IsaacNudeton/FBC-Semiconductor-System/docs/GAPS.md

# FBC System Gaps — Updated March 28, 2026

**FIRMWARE FEATURE-COMPLETE.** All Sonoma gaps closed. 79 wire codes, 43 tests, 0 warnings. Needs single JTAG deploy.

---

## Status Summary

| Category | Working (code) | Broken | Untested (needs hardware) | Missing |
|---|---|---|---|---|
| Protocol commands | 56 operations / 79 wire codes | 0 | DDR slots + test plan + IO bank + min/max (all code-complete) | 0 |
| AXI peripherals | 8 of 8 | 0 | 0 | 0 |
| Sensors | XADC (39.5°C verified) + MIN_MAX tracking | 0 | MIN_MAX on hardware | 0 |
| Storage | SD guarded | 0 | 0 | 0 |
| Thermal | Full loop: NTC → PID → DAC → FET | 0 | DAC output on real heater | 0 |
| V×I Power | read_core_power_mw() → feedforward | 0 | Actual current readings | 0 |
| DNA / MAC | 00:0A:35:C6:B4:2A verified | 0 | 0 | 0 |
| DDR Slots | Code complete (388 lines) | 0 | Hardware upload + run | 0 |
| Test Plan | Code complete (647 lines) | 0 | Autonomous execution | 0 |
| Undervoltage | Safety check added | 0 | Trip on real sag | 0 |
| IO Bank | IO_BANK_SET handler | 0 | I2C addr verification | 0 |
| GUI | wgpu native, 14 panels, switch | 0 | 0 | 0 |

---

## WORKING (16 commands, live-tested March 24)

Full command sweep on calibration board (12V/3A, calibration BIM connected via J3/J4/J5, no 48V/LCPS/DUT, EEPROM never programmed):

| Command | What it does | Verified | Notes |
|---|---|---|---|
| discover | Finds board, returns MAC/serial/version | March 24 | MAC 00:0A:35:AD:00:02 |
| ping | Round-trip latency | March 24 | 1.5ms RTT |
| status | 47-byte telemetry (state, cycles, errors, temp) | March 24 | Temp wrong (XADC bug) |
| firmware-info | Version, build date, serial, hw rev | March 24 | v1.0.0, serial 00000002 |
| vector-status | Vector engine state from AXI registers | March 24 | Idle, 0 vectors/errors |
| errors | Error log from BRAM (8 entries) | March 24 | All zeroed (correct) |
| analog | 32-channel ADC readings | March 24 | All 0mV (no DUT, expected) |
| log-info | Flight recorder metadata | March 24 | SD not present, 0 entries |
| vicor | 6-core status (all disabled — no 48V) | March 24 | Correct for cal board |
| eeprom | Read (safe empty — BIM present but EEPROM never programmed) | March 24 | Empty, expected |
| fastpins read | Read fast pin state | March 24 | din/dout/oen = 0x00000000 |
| set-fastpins | Write fast pin output + OEN | March 24 | Wrote 0xDEADBEEF |
| fastpins readback | **Round-trip verified** | March 24 | dout=0xDEADBEEF, oen=0xFFFFFFFF |
| configure | ACK received (clock write disabled) | March 24 | See bug #1b below |
| emergency-stop | Immediate ack | March 24 | |
| stop | Disables FBC decoder | March 24 | |

---

## BROKEN — NONE (all previously broken items fixed)

### ~~1. CONFIGURE (0x30) — clk_ctrl AXI crash~~ — ✅ FIXED March 25

- **Root cause:** Incomplete `case` statements in `clk_ctrl.v` AXI write FSM — missing `default:` arms for unhandled address ranges
- **Fix:** Added `default: ;` to both write case statements in `clk_ctrl.v`
- **Verified on hardware:** `configure --clock 3` succeeds, board survives
- **Bitstream rebuilt** with full timing closure (WNS=+0.018ns)

### ~~2. PAUSE (0xB5) / RESUME (0xB6)~~ — ✅ FIXED

- **Status:** Fully implemented and dispatched
- `handle_pause()` at `fbc_protocol.rs:1503` — disables FBC decoder, sets state to Paused
- `handle_resume()` at `fbc_protocol.rs:1512` — enables FBC decoder, sets state to Running
- Dispatched at `fbc_protocol.rs:1291-1292`

### ~~2b. PMBUS_STATUS_REQ (0x84)~~ — ✅ FIXED March 24

- **Was:** Command silently dropped (falls through to `_ => None`)
- **Fix:** Added dispatch arm + `handle_pmbus_status_req()`. Sets `pending_pmbus_status` flag, main.rs polls it, calls `psu_mgr.update_telemetry()`, builds response with per-supply address/bus/on/vout/iout.

### ~~2c. Vector LOAD/START/STOP (0xB2/0xB4/0xB7)~~ — ✅ FIXED March 24

- **Was:** Commands silently dropped (fall through to `_ => None`)
- **Fix:** Added dispatch arms:
  - LOAD (0xB2): Returns LOAD_ACK with status=0xFF (not fully implemented — needs SD-cached vector support)
  - START (0xB4): Delegates to `handle_start()` (same as runtime::START 0x40)
  - STOP (0xB7): Delegates to `handle_stop()` (same as runtime::STOP 0x41)
- No more silent drops — all commands get responses now

### ~~3. XADC — returns wrong values~~ — ✅ FIXED and VERIFIED March 25

- **Root cause:** u32 arithmetic overflow in `xadc.rs:242`. `raw * 503975` overflows u32 for any raw > 8522. Fixed: `as u32` → `as u64`.
- **Verified on hardware:** Reads 39.5°C (was -220°C). u64 overflow was the entire bug.
- **Thermal controller:** ONETWO crystallization feedforward deployed March 25, wired into main.rs safety loop. NTC formula upgraded (proper B-equation, Sonoma-matched divider).

---

## BROKEN (disabled/dead code)

### ~~4. SD Card — Data Abort~~ — ✅ FIXED March 24

- **Symptom:** `sd-repair` command crashes the board (ping fails after). Same crash expected for `sd-format` and `read-log`.
- **Original diagnosis (WRONG):** "byte writes to APB registers" — actually SD driver was already doing 32-bit RMW correctly
- **Real root cause:** `sd-repair` and `sd-format` called SD driver without checking if SD init succeeded. Using uninitialized SDHCI peripheral → Data Abort.
- **Fix:** Added `sd_init_ok` guard in `main.rs:394-420` — sd_format and sd_repair now check init status before touching SD hardware. Returns error status instead of crashing.
- **Impact:** SD commands now safe (return error when no SD card), flight recorder works when SD present

### 5. Firmware Update (BEGIN/CHUNK/COMMIT) — dead pipeline

- **Symptom:** Protocol handler parses packets and sets `pending_fw_begin`/`pending_fw_chunk` but main.rs never polls them
- **Impact:** Cannot update firmware over Ethernet, must use JTAG
- **Fix:** Add polling in main.rs + QSPI/NAND flash write logic (~100+ lines)
- **Blocks:** Production fleet management (44 boards per system)

---

## EXPECTED TIMEOUTS (not bugs — March 24 live test)

### pause / resume — timeout when not Running/Paused

- Handler returns `None` when state != Running (pause) or != Paused (resume)
- CLI gets timeout because no response packet is sent
- **Not a bug** — correct behavior, but CLI should print "Cannot pause: not running" instead of "Error: Timeout"

### pmbus-status (0x84) — no dispatch handler

- Falls through to `_ => None` in `process()` — see bug #2b above
- Expected timeout on hardware — confirmed March 24

### read-log — timeout when no SD card

- Handler tries to read SD sector, returns None or triggers SD access
- Expected timeout on calibration board (no SD card)

---

## UNTESTED (code exists, never run on hardware)

### 6. UPLOAD_VECTORS → DMA → FBC decoder (SUPERSEDED by DDR Slots)

- **Original path:** 64KB OCM buffer — limits to ~3K-65K vectors, too small for production
- **New path (March 26):** DDR slot upload (0x22) → 8 × 32MB DDR slots → `stream_from_ddr()` → fbc_dma → decoder
- **Status:** Code complete, needs hardware verification with actual .fbc file upload + vector execution
- **To verify:** `slot-upload 0 bringup_fast_pins.fbc` → `run-plan` → check decoder executes vectors

### 7. VICOR / PMBus power sequencing

- **Code path:** `handle_vicor_enable()`, `handle_power_sequence_on/off()`, `handle_pmbus_enable()`
- **Blocker:** Calibration board has no 48V supply, no LCPS connected
- **To verify:** Needs full system with power supplies

### 8. Pin configuration (io_config AXI peripheral)

- **Code path:** `fbc_loader.rs:configure_pins()` writes pin types to io_config at 0x4005_0000
- **Risk:** Never tested on hardware, pin types may not propagate to io_cell
- **To verify:** Load .fbc file with pin config section, read back pin types from AXI

---

## ~~MISSING (not implemented)~~ → IMPLEMENTED March 26

### ~~9. Burn-in orchestration~~ — ✅ DONE

**DDR Slot Table + Test Plan Executor** fully implemented in firmware + host + CLI:

```
1. Upload vectors → slot-upload (0x22) — .fbc to DDR slots (8 × 32MB)
2. Define plan   → set-plan (0x26) — multi-step: continuity → init → stress
3. Run plan      → run-plan (0x28) — firmware executes autonomously
4. Monitor       → plan-status (0x2A) — poll state/step/elapsed/errors
```

- **Firmware:** `ddr_slots.rs` (388 lines) + `testplan.rs` (647 lines) — PlanExecutor state machine
- **Host:** 6 new FbcClient methods + 6 new CLI commands
- **Checkpoint:** State persisted to DDR 0x0030_1000 every step transition (survives warm reset)
- **Per-step control:** fail_action (Abort/Continue), error_threshold, duration_secs
- **Loop support:** loop_start skips init/continuity on subsequent passes
- **Power sequencing** still handled by separate POWER_SEQ_ON/OFF commands before plan start

### ~~10. GUI profiling integration~~ — PARTIALLY DONE

**Native wgpu GUI (`app/`)** has dual-profile transport:
- `SystemType` enum in `host/src/types.rs` — Fbc, Sonoma, Hx, Xp160, Mcc, Shasta
- `transport.rs` dispatches by `BoardId::Mac` (FBC) vs `BoardId::Ip` (Sonoma)
- 37+ HwCommand variants covering both profiles + 7 switch commands
- 14 panels across 4 tabs (Dashboard, Profiling, Engineering, Datalogs)
- **Still missing:** HX (INSPIRE), XP-160/Shasta (INSPIRE), MCC (Modbus) transports

### ~~11. GUI ← host crate unification~~ — PARTIALLY DONE

**Native wgpu GUI (`app/`)** imports `fbc-host` crate directly.
The **Tauri GUI (`gui/`)** still has duplicate protocol code — but it's now reference only, not the product.
All new development targets the native `app/` which uses FbcClient + SonomaClient properly.

---

## FIXED (bugs found and patched during verification)

### 12. Error BRAM cycle read offset — ✅ FIXED March 24

- **Symptom:** Every error log entry had corrupted cycle timestamps
- **Root cause:** `regs.rs:576-577` read cycle count from offsets 0x1C/0x20, but RTL (`system_top.v:988-989`) provides cycle_lo at 0x18 and cycle_hi at 0x1C
- **Impact:** All error log cycle timestamps were garbage (reading vector number as cycle_lo, and out-of-range address as cycle_hi)
- **Fix:** Changed offsets to 0x18/0x1C in `ErrorBram::read_cycle()`

### 15. MAC collision (all boards identical) — ✅ FIXED March 24 (+ DNA guard March 25)

- **Symptom:** Every FBC board would get MAC `00:0A:35:AD:C0:90` — fatal for multi-board production with Cisco switch
- **Root cause:** `dna.rs:from_cpu_id()` read ARM MIDR (0xF8F00000) which returns 0x413FC090 on ALL Zynq 7020 silicon. `read_from_fpga()` returned `None` (unimplemented)
- **Impact:** Cisco switch can't distinguish boards. 44-board system completely broken
- **Fix:** Added `rtl/axi_device_dna.v` — reads 57-bit DNA_PORT silicon ID via 4-state FSM, exposes via AXI-Lite at 0x400A_0000 (DNA_LO/DNA_HI/DNA_STATUS). Firmware `dna.rs:read_from_fpga()` now reads real silicon DNA. Each board gets unique MAC `00:0A:35:{DNA}`. Wired into `system_top.v` AXI interconnect (8th peripheral)
- **Follow-up (March 25):** DNA peripheral not in March 12 bitstream — reading 0x400A_0000 caused AXI decode error → Data Abort → panic → GEM never initialized. Added FBC_CTRL version guard: if version=0 (old bitstream) or 0xFFFFFFFF (PL not ready), skip DNA read and fall back to CPU ID MAC. Unique per-board MAC requires bitstream rebuild with `axi_device_dna.v` included.

---

## KNOWN LIMITATIONS (bugs with architectural implications)

### 13. Vector data truncation — fast pins disconnected from test vectors

- **Symptom:** Fast pins (GPIO 128-159) never driven by test vectors
- **Root cause:** `axi_stream_fbc.v:59` extracts 128-bit payload from 256-bit AXI-Stream (`fbc_payload = s_axis_tdata[191:64]`). `fbc_decompress.rs:259` only copies 16 of 20 bytes into bytecode output, matching this 128-bit bus width.
- **Impact:** Only 128 BIM pins participate in vector tests. Fast pins require separate SET_PINS writes.
- **Options:** (A) Document as design constraint — fast pins are control-only, not vector-driven. (B) Firmware workaround: emit two SET_PINS per vector (128-bit + 32-bit). (C) RTL fix: widen AXI-Stream to 192 bits.
- **Current status:** Unresolved — needs architectural decision

### 14. PATTERN_REP -1 convention undocumented

- **Symptom:** `fbc_decompress.rs:273` subtracts 1 from repeat count (`count - 1`), `fbc_pkg.vh` doesn't document this encoding
- **Impact:** Off-by-one risk if encoders don't know repeat_count=N means N+1 repetitions
- **Fix:** Document convention in fbc_pkg.vh and PROTOCOL.md

---

## RTL Limitations (not bugs, design constraints)

### LOOP_N non-functional
- `fbc_decoder.v:126-128` counts iterations but has no instruction buffer/PC to replay loop body
- All loops must be unrolled in bytecode — tooling already does this
- Fix requires instruction FIFO (major RTL change)

### Phase clocks hardwired
- `clk_gen.v` CLKOUT5/6 fixed at 50MHz@90°/180°
- Don't follow freq_sel — pulse timing only correct at 50MHz
- Fix requires separate phase shifters per frequency

### 5 opcodes unimplemented
- SYNC, IMM32, IMM128, PATTERN_SEQ, SET_BOTH → S_ERROR in decoder
- SET_BOTH needs 256-bit payload but bus carries 128 bits
- Use SET_PINS + SET_OEN as two instructions instead

---

## Priority Order

```
PHASE 0: Rebuild & Package  ← CURRENT
│
├── 0a. Rebuild bitstream with axi_device_dna    [Vivado synthesis — all 8 AXI peripherals]
├── 0b. Package BOOT.BIN                         [bitstream + firmware ELF → single file]
└── 0c. Flash & power up                         [12V/3A → calibration board]

PHASE 1: First Vector Run
│
├── 1a. Discover board                           [verify DNA-based MAC works with new bitstream]
├── 1b. Upload bringup_fast_pins.fbc             [102 vectors, 5MHz, pins 128-159 OUTPUT]
├── 1c. Run vectors → read errors                [first GPIO toggle on real hardware]
├── 1d. Verify XADC temp reads ~42°C             [confirms u64 overflow fix]
└── 1e. Fix clk_ctrl AXI crash at 0x4008_0000    [probe via xsdb, blocks non-default clock]

PHASE 2: CLI orchestration
│
├── 2a. Full burn-in flow command                [configure → upload → run → errors → export]
├── 2b. DDR streaming for large vector files     [~100 lines redesign]
├── 2c. Sonoma burn-in flow via SSH              [verified against production ELFs]
└── 2d. Multi-board orchestration                [discover N boards, run same test on all]

PHASE 3: GUI unification + profiling
│
├── 3a. Import fbc-host crate into GUI           [replace fbc.rs/state.rs]
├── 3b. Add SystemType enum + profiles to GUI    [models + state]
├── 3c. Add Sonoma SSH transport in GUI backend  [SonomaClient]
├── 3d. Profile-driven UI adaptation             [React components]
└── 3e. Add HX/XP-160/MCC profiles to C engine  [dc_json.c]

PHASE 4: Production readiness (needs full system)
│
├── 4a. Test VICOR/PMBus power on real system    [needs 48V + LCPS]
├── 4b. Wire firmware update pipeline            [100+ lines + flash driver]
├── 4c. Thermal GPIO routing                     [identify HEATER_SW/COOLER_SW from J3c schematic]
└── 4d. Multi-board fleet management             [44-board coordination]

DONE (March 24-25):
├── ✅ Fix CONFIGURE polling, PAUSE/RESUME, PMBUS_STATUS, Vector LOAD/START/STOP dispatch
├── ✅ Fix XADC u64 overflow, SD guard, DNA guard, Error BRAM offset, MAC collision
├── ✅ NTC thermistor formula, thermal v2 wired, safety loop case temp
├── ✅ Compile-time thermal profiling (gen_fbc.c + compiler.rs, 25/25 tests)
├── ✅ Rust compiler CRC bug + emit_run off-by-one
├── ✅ Dead code cleanup (net.rs -268 lines), host/firmware warnings (0 warnings both crates)
└── ✅ Test vector: bringup_fast_pins.fbc (102 vectors, walking ones + checkerboard + toggle)
```
