IsaacNudeton/FBC-Semiconductor-System/docs/FIRST_LIGHT_SESSION.md

# First Light Session — March 2026

**Date:** March 2026  
**Duration:** ~8 hours  
**Result:** ✅ **FIRST LIGHT ACHIEVED** — Firmware running, ANNOUNCE packet sent

---

## Executive Summary

Bare-metal Rust firmware successfully booted on Zynq 7020 ARM Cortex-A9 via JTAG. All initialization completed, Ethernet initialized, ANNOUNCE broadcast packet transmitted.

**Key metrics:**
- CPU: 667 MHz (ARM PLL locked, FDIV=40)
- DDR: Initialized at 533 MHz
- FPGA PL: Responding (version 0x00010000)
- Ethernet: GEM0 TX/RX enabled, MAC 00:0A:35:AD:00:02
- Main loop: Running with IRQs enabled

---

## Bugs Fixed (10 Total)

### Bug #1: ITR Execution Ignored
**Symptom:** `exec_instr()` appeared to succeed but instructions didn't execute

**Root cause:** DBGDSCR bit 13 (ITRen) was never set. ARM TRM states "When ITRen=0, writes to DBGITR are silently ignored."

**Fix:** Added `_enable_itr()` method in `arm_loader.py`:
```python
def _enable_itr(self):
    dscr = self.read_dscr()
    if not (dscr & DSCR_ITREN):
        dscr |= DSCR_ITREN
        self.dbg_write(DBG_DSCR, dscr)
    # Drain stuck RXfull/TXfull
```

**File:** `arm_loader.py:420-440`

---

### Bug #2: Debug Register Address Space
**Symptom:** All debug register reads returned `0x00800052` (MEM-AP CSW echo)

**Root cause:** `0xF889xxxx` is CPU-private address space (only accessible by CPU itself). External debugger must use CoreSight debug AP via APB-AP at `0x80090000`.

**Fix:** Changed ALL debug register access to use APB-AP:
```python
DBG_CS_BASE = 0x8009_0000  # CoreSight CPU0 debug base (via APB-AP)

def dbg_read(self, offset):
    addr = DBG_CS_BASE + offset
    self.ap_write(AP_TAR, addr, apsel=1)
    return self.ap_read(AP_DRW, apsel=1)
```

**Files:** `arm_loader.py:175-195`, updated ~15 methods

---

### Bug #3: Resume → Immediate Re-Halt
**Symptom:** CPU restarted then immediately re-entered Debug state

**Root cause:** HDBGen (Halting Debug Enable) was still set when DRCR restart was written.

**Fix:** Clear HDBGen and ITRen BEFORE writing restart:
```python
def resume_cpu(self):
    self.dbg_write(DBG_DRCR, 0x1C)  # Clear sticky
    dscr = self.read_dscr()
    dscr &= ~DSCR_HDBGEN
    dscr &= ~DSCR_ITREN
    self.dbg_write(DBG_DSCR, dscr)
    self.dbg_write(DBG_DRCR, 0x2)  # Restart
```

**File:** `arm_loader.py:520-540`

---

### Bug #4: IRQ Storm Before main()
**Symptom:** CPU stuck in IRQ handler (`PC=0x00100064`) before reaching main loop

**Root cause:** CPSR had interrupts enabled when resuming. Pending IRQ fired before first instruction (`CPSID IF`) could execute.

**Fix:** Set CPSR to SVC mode with I+F bits disabled BEFORE BX:
```python
def set_pc_and_go(self, entry_addr):
    self.write_core_reg(0, 0xD3)  # SVC mode + I + F bits set
    self.exec_instr(MSR_CPSR_C(0))
    self.write_core_reg(0, entry_addr)
    self.exec_instr(BX(0))
    self.resume_cpu()
```

**File:** `arm_loader.py:560-580`

---

### Bug #5: Missing PS Peripheral Init
**Symptom:** `GEM0_NET_CTRL = 0x00000000` (Ethernet never enabled)

**Root cause:** MIO pins not configured for RGMII, peripheral clocks not enabled. Firmware expected FSBL to do this, but we're bypassing FSBL.

**Fix:** Extracted PS7 init tables from Vivado `ps7_init.c`:
- `PS7_CLK_INIT` (11 entries) — Clock enables/dividers
- `PS7_MIO_INIT` (55 entries) — MIO pin muxing
- `PS7_PERIPH_INIT` (5 entries) — UART/GEM config

**File:** `arm_loader.py:67-250`, `init_ps_peripherals()`

---

### Bug #6: ARM PLL Not Configured
**Symptom:** CPU running at 33 MHz instead of 667 MHz (20x slower)

**Root cause:** Boot ROM leaves ARM PLL at default (FDIV=26). Firmware delay loops calibrated for 667 MHz, taking 20x longer.

**Fix:** Added ARM PLL init sequence:
```python
ARM_PLL_INIT = [
    (0xF8000110, 0x003FFFF0, 0x000FA220),  # ARM_PLL_CFG
    (0xF8000100, 0x0007F000, 0x00028000),  # ARM_PLL_CTRL: FDIV=40
    (0xF8000100, 0x00000010, 0x00000010),  # BYPASS=1
    (0xF8000100, 0x00000001, 0x00000001),  # RESET=1
    (0xF8000100, 0x00000001, 0x00000000),  # RESET=0
    # Poll 0xF800010C bit 0 for ARM_PLL_LOCK
    (0xF8000100, 0x00000010, 0x00000000),  # BYPASS=0
]
```

**File:** `arm_loader.py:67-83`, `init_ps_peripherals():1270-1290`

---

### Bug #7: IO PLL Not Configured
**Symptom:** Peripheral clocks wrong frequency (GEM, UART, FCLK)

**Root cause:** IO PLL provides 1000 MHz source for peripherals. Without init, running at boot ROM default.

**Fix:** Added IO PLL init (FDIV=30 → 1000 MHz):
```python
IO_PLL_INIT = [
    (0xF8000118, 0x003FFFF0, 0x001452C0),  # IO_PLL_CFG
    (0xF8000108, 0x0007F000, 0x0001E000),  # IO_PLL_CTRL: FDIV=30
    # ... bypass/reset sequence
]
```

**File:** `arm_loader.py:85-95`, `init_ps_peripherals():1290-1305`

---

### Bug #8: XADC Register Offsets Wrong
**Symptom:** XADC reads 0mV → `hang_with_blink(2)` (VCCINT < 900)

**Root cause:** Firmware had wrong offsets:
- MSTS: `0x10` → should be `0x0C`
- CMDFIFO: `0x14` → should be `0x10`
- RDFIFO: `0x18` → should be `0x14`
- MCTL: `0x1C` → should be `0x18`

**Fix:** Corrected offsets in `xadc.rs`:
```rust
pub const MSTS: usize = 0x0C;      // Was 0x10
pub const CMDFIFO: usize = 0x10;   // Was 0x14
pub const RDFIFO: usize = 0x14;    // Was 0x18
pub const MCTL: usize = 0x18;      // Was 0x1C
```

**File:** `firmware/src/hal/xadc.rs:22-25`

---

### Bug #9: Stuck in IRQ Handler (Data Abort)
**Symptom:** PC stuck at `0x00100064` for 30+ seconds

**Root cause:** GIC not initialized yet, but peripheral (SDIO/GPIO) fired interrupt during init. Handler called `gic_irq_dispatch()` which hung on uninitialized GIC registers.

**Fix:** Disable GIC at hardware level BEFORE firmware starts:
```python
# In arm_loader.py set_pc_and_go():
self.mem_write(0xF8F01000, 0)  # GICD_CTLR = 0 (disable distributor)
self.mem_write(0xF8F00100, 0)  # GICC_CTLR = 0 (disable CPU interface)
for i in range(3):
    self.mem_write(0xF8F01180 + i*4, 0xFFFFFFFF)  # Disable all IRQs
    self.mem_write(0xF8F01280 + i*4, 0xFFFFFFFF)  # Clear all pending
```

**File:** `arm_loader.py:1365-1373`

---

### Bug #10: I-Cache Disabled (100x Slow)
**Symptom:** Firmware running but ~100x slower than expected

**Root cause:** `disable_mmu_caches()` turned off I-cache. Every instruction fetch went to DDR (~100ns vs ~1ns cache hit).

**Fix:** Enable I-cache in `boot.S` after MMU disable:
```assembly
/* Enable I-cache for performance (no MMU needed) */
mov     r0, #0
mcr     p15, 0, r0, c7, c5, 0   /* ICIALLU: invalidate I-cache */
dsb
isb
mrc     p15, 0, r0, c1, c0, 0   /* Read SCTLR */
orr     r0, r0, #(1 << 12)      /* Set I bit (I-cache enable) */
bic     r0, r0, #(1 << 0)       /* Ensure MMU stays off */
mcr     p15, 0, r0, c1, c0, 0   /* Write SCTLR */
isb
```

**File:** `firmware/src/boot.S:61-72`

---

## Additional Infrastructure Added

### OCM Remap for DMA Buffers
**Problem:** GEM0 DMA descriptors linked at `0xFFFC0000` (OCM HIGH), but after reset OCM is at LOW (`0x00000000`).

**Fix:** Remap OCM to high address:
```python
def init_ocm(self):
    cfg = self.mem_read(0xF8006080)  # OCM_CFG
    self.mem_write(0xF8006080, cfg | 0xF)  # Remap to 0xFFFC0000
```

**File:** `arm_loader.py:1340-1360`

### PS-PL Interface Enable
**Problem:** AXI GP0 access caused Data Abort without level shifter enable.

**Fix:** Enable level shifters + deassert FPGA resets:
```python
def init_ps_pl(self):
    self.mem_write(0xF8000900, 0x0F)  # LVL_SHFTR_EN
    self.mem_write(0xF8000240, 0x00)  # FPGA_RST_CTRL
```

**File:** `arm_loader.py:1380-1400`

---

## Final Working State

```
CPU:        Cortex-A9 @ 667 MHz (ARM PLL: 1333 MHz / 2)
DDR:        533 MHz (3x), 355 MHz (2x)
IO PLL:     1000 MHz (source for GEM, UART, FCLK)
FPGA PL:    Version 0x00010000 (responding via AXI GP0)
Ethernet:   GEM0 enabled (NET_CTRL = 0x1C)
            MAC: 00:0A:35:AD:00:02
            TX: 1 broadcast (64 bytes) — ANNOUNCE sent!
            RX: 0 frames (no one talking yet)
GIC:        Initialized, IRQs enabled in main loop
OCM:        Remapped to 0xFFFC0000 (DMA descriptors)
PS-PL:      Level shifters enabled, AXI GP0 accessible
```

---

## Methodology

### Debugging Approach
1. **Read registers first** — Never guess, always measure
2. **Single-step when stuck** — Halt, read PC/LR/SP, disassemble
3. **Check exception state** — CPSR/SPSR reveal what exception fired
4. **Verify assumptions** — "The CPU is in IRQ handler" → actually Data Abort
5. **Hardware-level fixes** — When software fails, disable hardware (GIC)

### Key Tools
- `arm_loader.py status` — Full CPU state dump
- `arm_loader.py read <addr>` — Memory/peripheral inspection
- `arm-none-eabi-objdump -d` — Disassembly
- Wireshark — Packet capture (filter: `eth.type == 0x88b5`)

---

## Lessons Learned

### 1. ARM Debug Architecture is Non-Obvious
- CPU-private debug regs (`0xF889xxxx`) NOT accessible from external debugger
- Must use CoreSight debug AP via APB-AP (`0x80090000`)
- PC reads as `instruction_addr + 8` in debug state
- SPSR reveals exception mode, not current mode

### 2. Zynq PS Init is Complex
- FSBL does ~1000 register writes before jumping to app
- Bypassing FSBL means replicating ALL of it:
  - PLL init (ARM, DDR, IO)
  - Clock dividers
  - MIO pin muxing
  - Peripheral enables
  - PS-PL interface
  - OCM remap

### 3. Interrupts Must Be Disabled Until GIC Ready
- Classic embedded bug: enabling IRQs before interrupt controller initialized
- Fix: Disable at BOTH CPSR level AND GIC hardware level
- Re-enable only AFTER GIC distributor + CPU interface initialized

### 4. Cache Matters
- Without I-cache: 100x slowdown (DDR latency vs cache hit)
- Can enable I-cache without MMU (instruction fetch only)
- Must invalidate before enabling

---

## Files Modified

| File | Lines Changed | Purpose |
|---|---|---|
| `arm_loader.py` | ~400 | JTAG loader, PS init, GIC disable, OCM remap |
| `firmware/src/boot.S` | 13 | I-cache enable |
| `firmware/src/hal/xadc.rs` | 4 | Register offset fix |
| `firmware/src/main.rs` | 12 | IRQ disable at entry, safety checks disabled |

---

## Next Steps

1. **GUI Discovery** — Run `npm run tauri dev`, click "Discover Boards"
2. **Upload Vectors** — Use GUI to upload `.fbc` pattern
3. **Run Test** — Start burn-in test, verify error capture
4. **Re-enable Safety** — Fix XADC properly, re-enable voltage checks
5. **SD Card** — Fix alignment fault, enable SD card boot
6. **Standalone Boot** — Create BOOT.BIN, test without JTAG

---

## Session Participants

- **Isaac** — Hardware, debugging, persistence
- **Claude** — Debugging session, ARM architecture, GIC fix
- **Qwen** — Documentation, final verification

---

**Date Achieved:** March 2026  
**Time to First Light:** ~8 hours  
**Bugs Fixed:** 10  
**Packets Transmitted:** 1 (ANNOUNCE)  
**Status:** ✅ **HISTORIC MILESTONE ACHIEVED**
