IsaacNudeton/FBC-Semiconductor-System/firmware/src/hal/eeprom.rs

//! 24LC02 I2C EEPROM Driver
//!
//! Driver for 256-byte I2C EEPROM used for BIM configuration storage.
//!
//! # Hardware
//! - Device: 24LC02BHT-I/LT (Microchip)
//! - Capacity: 256 bytes (2 Kbit)
//! - Page size: 8 bytes
//! - Write time: 5ms max per page
//! - Interface: I2C, 400 kHz
//!
//! # EEPROM Layout
//!
//! ```text
//! 0x00-0x0F: Header (16 bytes)
//! 0x10-0x4F: Power rail config (64 bytes)
//! 0x50-0x8F: Calibration data (64 bytes)
//! 0x90-0xEF: DUT metadata (96 bytes)
//! 0xF0-0xF7: Statistics (8 bytes)
//! 0xF8-0xFB: CRC32 checksum (4 bytes)
//! 0xFC-0xFF: Reserved (4 bytes)
//! ```

use super::{I2c, I2cError, Gpio, MioPin, delay_ms};

/// EEPROM size in bytes
pub const EEPROM_SIZE: usize = 256;

/// EEPROM page size (write granularity)
const PAGE_SIZE: usize = 8;

/// Write cycle time in milliseconds
const WRITE_CYCLE_MS: u32 = 5;

/// Default I2C address (A0 = 0)
pub const EEPROM_ADDR: u8 = 0x50;

/// EEPROM error types
#[derive(Debug, Clone, Copy, PartialEq, Eq)]
pub enum EepromError {
    /// I2C communication error
    I2c(I2cError),
    /// Invalid EEPROM address
    InvalidAddress,
    /// Write verification failed
    VerifyFailed,
    /// Invalid checksum
    ChecksumMismatch,
    /// Invalid magic number (EEPROM not programmed)
    InvalidMagic,
}

impl From<I2cError> for EepromError {
    fn from(e: I2cError) -> Self {
        EepromError::I2c(e)
    }
}

/// 24LC02 EEPROM driver
///
/// Supports optional Write Protect (WP) pin control. The WP pin on 24LC02:
/// - HIGH = Write protected (reads only)
/// - LOW = Write enabled
///
/// BIM Hardware Notes:
/// - Most BIMs (e.g., Normandy) use a **jumper header** for WP control, not GPIO.
///   The jumper (J152 on Normandy) selects write-enable or write-protect.
/// - If WP is tied to GND on the hardware, no GPIO is needed - use `new()`.
/// - If WP is connected to a GPIO (rare), pass it to `with_wp_pin()`.
pub struct Eeprom<'a> {
    i2c: &'a I2c,
    addr: u8,
    /// Optional GPIO controller for WP pin
    gpio: Option<&'a Gpio>,
    /// Optional WP pin number (MIO)
    wp_pin: Option<MioPin>,
}

impl<'a> Eeprom<'a> {
    /// Create new EEPROM instance (no WP pin control)
    ///
    /// Use this if WP is tied to GND on the hardware (most common).
    ///
    /// # Arguments
    /// * `i2c` - I2C peripheral instance
    /// * `addr` - Device I2C address (0x50-0x57 depending on A0-A2 pins)
    pub const fn new(i2c: &'a I2c, addr: u8) -> Self {
        Self { i2c, addr, gpio: None, wp_pin: None }
    }

    /// Create new EEPROM instance with WP pin control
    ///
    /// Use this if WP is connected to a GPIO on the hardware.
    ///
    /// # Arguments
    /// * `i2c` - I2C peripheral instance
    /// * `addr` - Device I2C address (0x50-0x57 depending on A0-A2 pins)
    /// * `gpio` - GPIO controller
    /// * `wp_pin` - MIO pin connected to EEPROM WP
    pub const fn with_wp_pin(i2c: &'a I2c, addr: u8, gpio: &'a Gpio, wp_pin: MioPin) -> Self {
        Self { i2c, addr, gpio: Some(gpio), wp_pin: Some(wp_pin) }
    }

    /// Enable writes by driving WP LOW
    fn enable_writes(&self) {
        if let (Some(gpio), Some(pin)) = (self.gpio, self.wp_pin) {
            gpio.set_output(pin);
            gpio.write_pin(pin, false);  // LOW = write enabled
            delay_ms(1);  // Allow pin to settle
        }
    }

    /// Disable writes by driving WP HIGH
    fn disable_writes(&self) {
        if let (Some(gpio), Some(pin)) = (self.gpio, self.wp_pin) {
            gpio.write_pin(pin, true);  // HIGH = write protected
        }
    }

    /// Read a single byte from EEPROM
    ///
    /// # Arguments
    /// * `address` - EEPROM address (0-255)
    pub fn read_byte(&self, address: u8) -> Result<u8, EepromError> {
        if address as usize >= EEPROM_SIZE {
            return Err(EepromError::InvalidAddress);
        }

        let mut buf = [0u8; 1];
        self.i2c.write_read(self.addr, &[address], &mut buf)?;
        Ok(buf[0])
    }

    /// Write a single byte to EEPROM
    ///
    /// # Arguments
    /// * `address` - EEPROM address (0-255)
    /// * `data` - Byte to write
    pub fn write_byte(&self, address: u8, data: u8) -> Result<(), EepromError> {
        if address as usize >= EEPROM_SIZE {
            return Err(EepromError::InvalidAddress);
        }

        // Enable writes (if WP pin is controlled)
        self.enable_writes();

        // Write byte
        let result = self.i2c.write(self.addr, &[address, data]);

        // Wait for write cycle to complete
        delay_ms(WRITE_CYCLE_MS);

        // Disable writes (if WP pin is controlled)
        self.disable_writes();

        // Check I2C result
        result?;

        // Verify write
        let verify = self.read_byte(address)?;
        if verify != data {
            return Err(EepromError::VerifyFailed);
        }

        Ok(())
    }

    /// Read sequential bytes from EEPROM
    ///
    /// # Arguments
    /// * `address` - Starting EEPROM address
    /// * `buf` - Buffer to store read data
    pub fn read(&self, address: u8, buf: &mut [u8]) -> Result<(), EepromError> {
        if address as usize + buf.len() > EEPROM_SIZE {
            return Err(EepromError::InvalidAddress);
        }

        // Set address pointer, then read sequentially
        self.i2c.write_read(self.addr, &[address], buf)?;
        Ok(())
    }

    /// Write sequential bytes to EEPROM (page-aware)
    ///
    /// This handles page boundaries automatically. The 24LC02 has 8-byte pages,
    /// and writes must not cross page boundaries.
    ///
    /// # Arguments
    /// * `address` - Starting EEPROM address
    /// * `data` - Data to write
    pub fn write(&self, address: u8, data: &[u8]) -> Result<(), EepromError> {
        if address as usize + data.len() > EEPROM_SIZE {
            return Err(EepromError::InvalidAddress);
        }

        // Enable writes (if WP pin is controlled)
        self.enable_writes();

        let mut offset = 0;
        let mut current_addr = address as usize;
        let mut result: Result<(), EepromError> = Ok(());

        while offset < data.len() {
            // Calculate bytes remaining in current page
            let page_start = current_addr & !(PAGE_SIZE - 1);  // Align to page boundary
            let page_end = page_start + PAGE_SIZE;
            let bytes_in_page = page_end - current_addr;
            let bytes_to_write = core::cmp::min(bytes_in_page, data.len() - offset);

            // Build write command: [address, data...]
            let mut write_buf = [0u8; PAGE_SIZE + 1];  // Max page size + address byte
            write_buf[0] = current_addr as u8;
            write_buf[1..1 + bytes_to_write].copy_from_slice(&data[offset..offset + bytes_to_write]);

            // Write page
            if let Err(e) = self.i2c.write(self.addr, &write_buf[..1 + bytes_to_write]) {
                result = Err(e.into());
                break;
            }

            // Wait for write cycle
            delay_ms(WRITE_CYCLE_MS);

            offset += bytes_to_write;
            current_addr += bytes_to_write;
        }

        // Disable writes (if WP pin is controlled) - do this before verification
        self.disable_writes();

        // Check for I2C errors
        result?;

        // Verify all written data
        let mut verify_buf = [0u8; EEPROM_SIZE];
        self.read(address, &mut verify_buf[..data.len()])?;
        if verify_buf[..data.len()] != *data {
            return Err(EepromError::VerifyFailed);
        }

        Ok(())
    }

    /// Read entire EEPROM contents
    pub fn read_all(&self, buf: &mut [u8; EEPROM_SIZE]) -> Result<(), EepromError> {
        self.read(0, buf)
    }

    /// Write entire EEPROM contents
    pub fn write_all(&self, data: &[u8; EEPROM_SIZE]) -> Result<(), EepromError> {
        self.write(0, data)
    }

    /// Erase EEPROM (write all 0xFF)
    pub fn erase(&self) -> Result<(), EepromError> {
        let empty = [0xFFu8; EEPROM_SIZE];
        self.write_all(&empty)
    }
}

/// CRC32 lookup table (IEEE 802.3 polynomial: 0xEDB88320)
const CRC32_TABLE: [u32; 256] = generate_crc32_table();

/// Generate CRC32 lookup table at compile time
const fn generate_crc32_table() -> [u32; 256] {
    let mut table = [0u32; 256];
    let mut i = 0;
    while i < 256 {
        let mut crc = i as u32;
        let mut j = 0;
        while j < 8 {
            if crc & 1 != 0 {
                crc = (crc >> 1) ^ 0xEDB88320;
            } else {
                crc >>= 1;
            }
            j += 1;
        }
        table[i] = crc;
        i += 1;
    }
    table
}

/// Calculate CRC32 checksum
pub fn crc32(data: &[u8]) -> u32 {
    let mut crc = 0xFFFFFFFFu32;
    for &byte in data {
        let index = ((crc ^ byte as u32) & 0xFF) as usize;
        crc = (crc >> 8) ^ CRC32_TABLE[index];
    }
    !crc
}

/// BIM type identifiers
#[derive(Debug, Clone, Copy, PartialEq, Eq)]
#[repr(u8)]
pub enum BimType {
    Unknown = 0x00,
    Normandy = 0x01,
    SyrosV2 = 0x02,
    Aurora = 0x03,
    Iliad = 0x04,
    // Add more as needed
}

impl BimType {
    /// Convert from u8
    pub fn from_u8(val: u8) -> Self {
        match val {
            0x01 => BimType::Normandy,
            0x02 => BimType::SyrosV2,
            0x03 => BimType::Aurora,
            0x04 => BimType::Iliad,
            _ => BimType::Unknown,
        }
    }

    /// Get human-readable name
    pub fn name(&self) -> &'static str {
        match self {
            BimType::Unknown => "Unknown",
            BimType::Normandy => "Normandy",
            BimType::SyrosV2 => "Syros v2",
            BimType::Aurora => "Aurora",
            BimType::Iliad => "Iliad",
        }
    }
}

/// Sensor type for thermal measurement
#[derive(Debug, Clone, Copy, PartialEq, Eq)]
#[repr(u8)]
pub enum SensorType {
    Ntc30k = 0,    // 30kΩ NTC (B=3985.3) — Sonoma default
    Ntc10k = 1,    // 10kΩ NTC (B=3492.0)
    Diode = 2,     // Linear diode sensor
}

/// Cooling type
#[derive(Debug, Clone, Copy, PartialEq, Eq)]
#[repr(u8)]
pub enum CoolingType {
    Air = 0,
    Water = 1,
}

/// Power rail configuration — self-describing with channel ID
///
/// Each rail identifies itself by PMBus channel number (1-24).
/// channel_id=0xFF means the slot is unused/disabled.
/// Works for LCPS (J6 ch 1-8, J7 ch 9-16) and HCPS (ch 17-24).
#[derive(Debug, Clone, Copy)]
#[repr(C, packed)]
pub struct RailConfig {
    /// PMBus channel number (1-24). 0xFF = disabled/unused slot.
    pub channel_id: u8,
    /// Flags: bit 0 = is_hcps (high current), bit 1 = monitored (ADC readback)
    pub flags: u8,
    /// Maximum safe voltage in millivolts (overvoltage shutdown threshold)
    pub max_voltage_mv: u16,
    /// Minimum safe voltage in millivolts (brownout detection threshold)
    pub min_voltage_mv: u16,
    /// Maximum current in milliamps (overcurrent shutdown threshold)
    pub max_current_ma: u16,
}

impl RailConfig {
    /// Rail flag: this is a High Current Power Supply
    pub const FLAG_HCPS: u8 = 0x01;
    /// Rail flag: this rail has ADC monitoring (voltage/current readback)
    pub const FLAG_MONITORED: u8 = 0x02;

    pub const fn disabled() -> Self {
        Self {
            channel_id: 0xFF,
            flags: 0,
            max_voltage_mv: 0,
            min_voltage_mv: 0,
            max_current_ma: 0,
        }
    }

    /// Check if this rail slot is active (has a valid channel assignment)
    pub const fn is_active(&self) -> bool {
        self.channel_id != 0xFF && self.channel_id != 0
    }

    /// Check if this is an HCPS rail
    pub const fn is_hcps(&self) -> bool {
        self.flags & Self::FLAG_HCPS != 0
    }

    /// Derive nominal voltage as midpoint of limits (for display only)
    pub const fn nominal_mv(&self) -> u16 {
        if self.max_voltage_mv == 0 {
            0
        } else {
            (self.max_voltage_mv + self.min_voltage_mv) / 2
        }
    }
}

/// Thermal configuration stored in EEPROM
#[derive(Debug, Clone, Copy)]
#[repr(C, packed)]
pub struct ThermalConfig {
    /// Temperature setpoint in 0.1°C units (e.g., 1250 = 125.0°C)
    pub setpoint_dc: i16,
    /// Sensor type (0=NTC30k, 1=NTC10k, 2=diode)
    pub sensor_type: u8,
    /// Cooling type (0=air, 1=water)
    pub cooling_type: u8,
    /// MIO pin number for heater FET control (0xFF = unknown/not routed)
    pub heater_pin: u8,
    /// MIO pin number for cooler/fan FET control (0xFF = unknown/not routed)
    pub fan_pin: u8,
}

impl ThermalConfig {
    pub const fn default() -> Self {
        Self {
            setpoint_dc: 1250,  // 125.0°C default
            sensor_type: 0,     // NTC 30kΩ
            cooling_type: 0,    // Air
            heater_pin: 0xFF,   // Unknown
            fan_pin: 0xFF,      // Unknown
        }
    }
}

/// Number of power rail slots in EEPROM
pub const NUM_EEPROM_RAILS: usize = 16;

/// BIM EEPROM data structure v2 (256 bytes total)
///
/// # Layout
///
/// ```text
/// 0x00-0x0F: Header (16 bytes)
/// 0x10-0x8F: Power rails[16] × RailConfig (128 bytes)
/// 0x90-0xCF: Calibration data (64 bytes)
/// 0xD0-0xD7: Project ID (8 bytes)
/// 0xD8-0xD9: BIM number (2 bytes)
/// 0xDA-0xDF: Thermal config (6 bytes)
/// 0xE0-0xE7: Statistics (8 bytes)
/// 0xE8-0xF7: Reserved (16 bytes)
/// 0xF8-0xFB: CRC32 checksum (4 bytes)
/// 0xFC-0xFF: Reserved (4 bytes)
/// ```
///
/// ## Power Rails
///
/// 16 self-describing slots. Each RailConfig has a channel_id field (1-24)
/// so LCPS J6 (ch 1-8), LCPS J7 (ch 9-16), and HCPS (ch 17-24) can be
/// mixed freely. Unused slots have channel_id=0xFF.
///
/// ## Project ID
///
/// Short code (e.g., "S0026") that maps to the LRM database for full
/// customer/device/test plan info. The board doesn't need strings —
/// the host does the lookup.
#[derive(Debug, Clone, Copy)]
#[repr(C, packed)]
pub struct BimEeprom {
    // ===== HEADER (16 bytes) =====
    /// Magic number: 0xBEEFCAFE indicates programmed EEPROM
    pub magic: u32,

    /// EEPROM format version (current: 2)
    pub version: u8,

    /// BIM type identifier
    pub bim_type: u8,

    /// Hardware revision
    pub hw_revision: u8,

    /// Reserved byte
    /// Rack position is determined by Ethernet cable, not stored in EEPROM.
    pub _reserved_header: u8,

    /// Unique serial number (board DNA or assigned serial)
    pub serial_number: u32,

    /// Manufacturing date (Unix timestamp)
    pub manufacture_date: u32,

    // ===== POWER RAIL CONFIG (128 bytes) =====
    /// 16 self-describing power rails (LCPS J6/J7 + HCPS, any order)
    /// Each rail has channel_id (1-24) to identify which PMBus address.
    /// channel_id=0xFF means slot is unused.
    pub rails: [RailConfig; NUM_EEPROM_RAILS],  // 16 * 8 = 128 bytes

    // ===== CALIBRATION DATA (64 bytes) =====
    /// Voltage calibration offset in mV (signed), channels 0-15
    pub voltage_cal: [i16; 16],  // 16 * 2 = 32 bytes

    /// Current calibration offset in mA (signed), channels 0-15
    pub current_cal: [i16; 16],  // 16 * 2 = 32 bytes

    // ===== PROJECT ID (10 bytes) =====
    /// Project code for LRM database lookup (null-terminated ASCII, e.g., "S0026")
    pub project_code: [u8; 8],

    /// Which BIM in the production batch (e.g., 17 of 40)
    pub bim_number: u16,

    // ===== THERMAL CONFIG (6 bytes) =====
    /// Thermal configuration (setpoint, sensor, cooling, GPIO pins)
    pub thermal: ThermalConfig,

    // ===== STATISTICS (8 bytes) =====
    /// Number of times reprogrammed
    pub program_count: u16,

    /// BIM asset ID / inventory tag (null-terminated, e.g., "BIM-042")
    pub bim_asset_id: [u8; 6],

    // ===== RESERVED (16 bytes) =====
    pub _reserved2: [u8; 16],

    // ===== CHECKSUM (4 bytes) =====
    /// CRC32 of bytes 0x00-0xF7 (everything except checksum + final reserved)
    pub checksum: u32,

    // ===== RESERVED (4 bytes) =====
    pub _reserved3: [u8; 4],
}

// Compile-time assertion that BimEeprom is exactly 256 bytes
const _: () = assert!(core::mem::size_of::<BimEeprom>() == 256);
// Compile-time assertion that RailConfig is exactly 8 bytes
const _: () = assert!(core::mem::size_of::<RailConfig>() == 8);
// Compile-time assertion that ThermalConfig is exactly 6 bytes
const _: () = assert!(core::mem::size_of::<ThermalConfig>() == 6);
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
